ollyoid/TuneShroom/images/IMG_20191014_210542.jpg

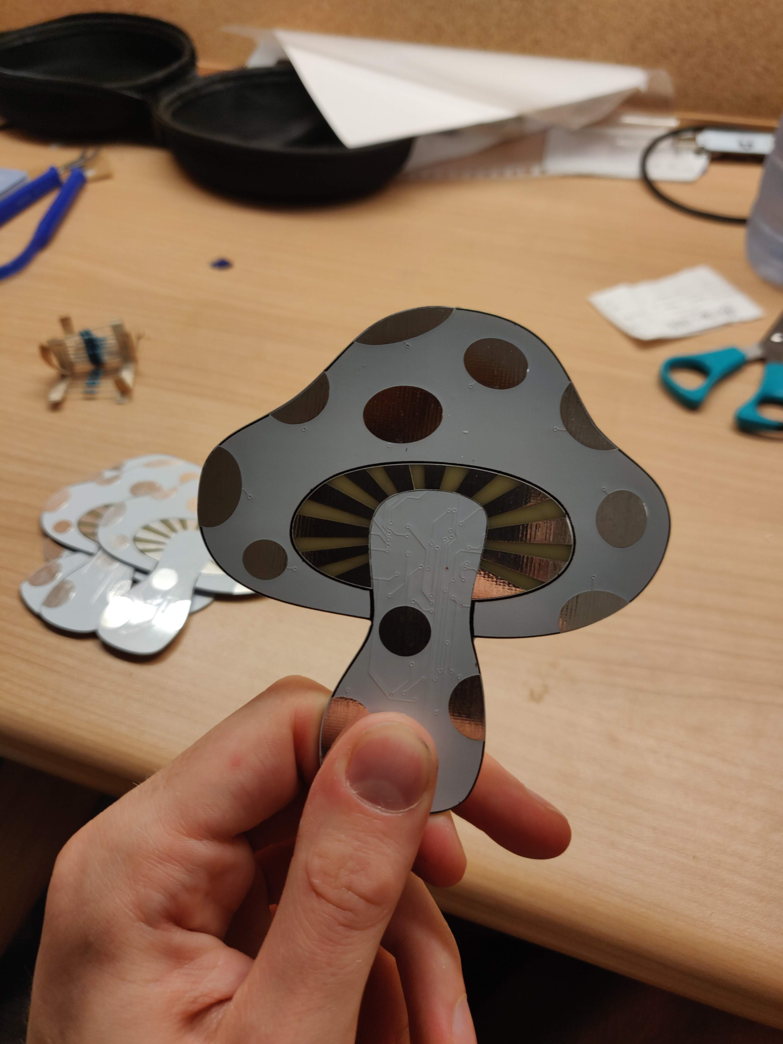
images/IMG_20191014_210542.jpg
