ollyoid/TuneShroom/images/IMG_20191022_233444.jpg

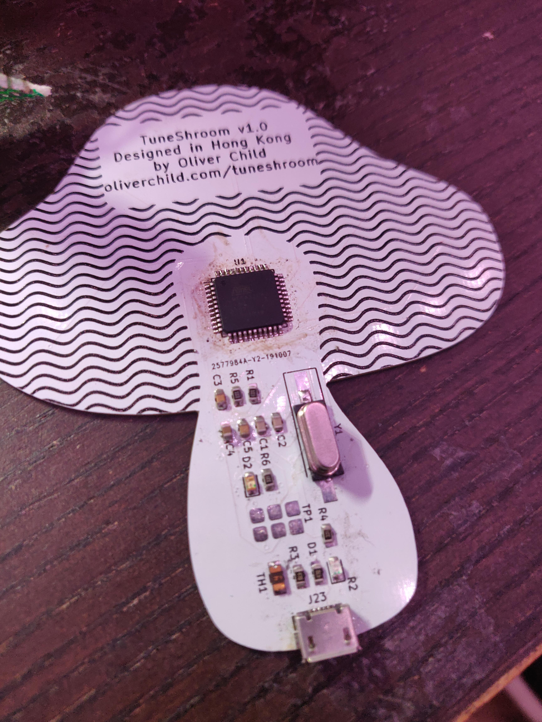
images/IMG_20191022_233444.jpg
